atarola/compy6502/kicad/console/console.kicad_pcb

## KiCad design Arquivos Kicad/Power.kicad_sch

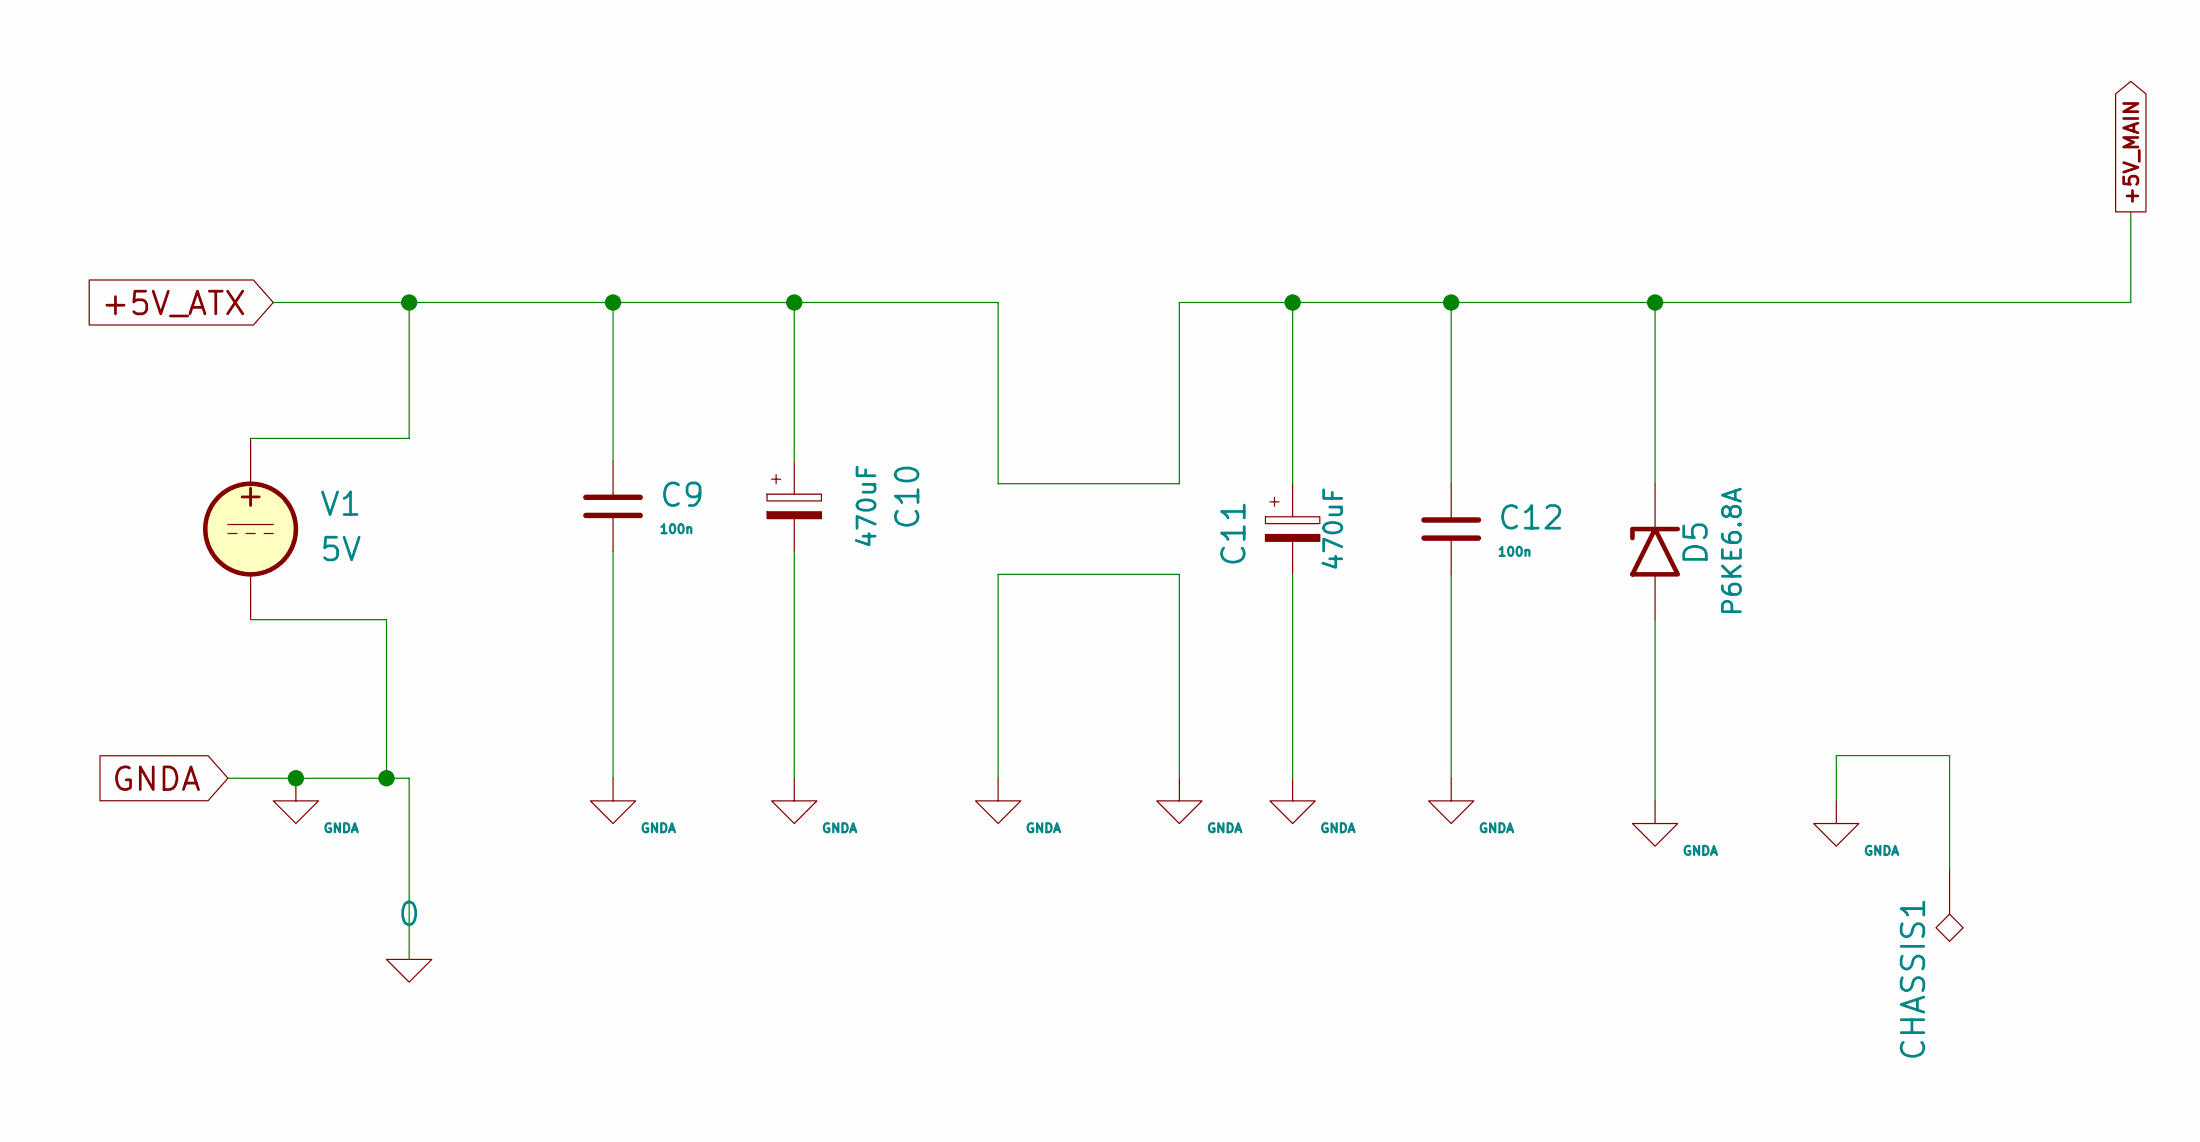
[picture p4: schematic Power.kicad_sch]

Parts:
C9, C12: 100n
C10, C11: 470uF
CHASSIS1: TestPoint_Alt
D5: P6KE6.8A; D_P600_R-6_P20.00mm_Horizontal
V1: 5V

Connections:
0: C9.2, C10.2, C11.2, C12.2, CHASSIS1.1, D5.2 (A2), V1.2
+5V_ATX: C9.1, C10.1, C11.1, C12.1, D5.1 (A1), V1.1
